maciejmiklas/led-clock/TempSensor.h

/*
 * Licensed to the Apache Software Foundation (ASF) under one or more
 * contributor license agreements.  See the NOTICE file distributed with
 * this work for additional information regarding copyright ownership.
 * The ASF licenses this file to You under the Apache License, Version 2.0
 * (the "License"); you may not use this file except in compliance with
 * the License.  You may obtain a copy of the License at
 *
 *      http://www.apache.org/licenses/LICENSE-2.0
 *
 * Unless required by applicable law or agreed to in writing, software
 * distributed under the License is distributed on an "AS IS" BASIS,
 * WITHOUT WARRANTIES OR CONDITIONS OF ANY KIND, either express or implied.
 * See the License for the specific language governing permissions and
 * limitations under the License.
 */
#ifndef TEMPSENSOR_H_
#define TEMPSENSOR_H_

#include "Arduino.h"
#include "OneWire.h"
#include "DallasTemperature.h"
#include "ArdLog.h"
#include "DispUtil.h"

class TempSensor {
public:
	TempSensor();
	float getTemp();
	void cycle();

private:
	constexpr static float READ_ADJUST = 0.0f;
	const static uint8_t DIG_PIN_TEMP_SENSOR = 44;
	const static uint16_t PROBE_FREQ_MS = 10000;

	float curentTemp;
	uint32_t lastProbeTime;
	OneWire oneWire;
	DallasTemperature dallasTemperature;

	inline void readTemp();
	void init();
};

#endif /* TEMPSENSOR_H_ */
