maciejmiklas/led-clock/WeatherDisplay.cpp

/*
 * Licensed to the Apache Software Foundation (ASF) under one or more
 * contributor license agreements.  See the NOTICE file distributed with
 * this work for additional information regarding copyright ownership.
 * The ASF licenses this file to You under the Apache License, Version 2.0
 * (the "License"); you may not use this file except in compliance with
 * the License.  You may obtain a copy of the License at
 *
 *      http://www.apache.org/licenses/LICENSE-2.0
 *
 * Unless required by applicable law or agreed to in writing, software
 * distributed under the License is distributed on an "AS IS" BASIS,
 * WITHOUT WARRANTIES OR CONDITIONS OF ANY KIND, either express or implied.
 * See the License for the specific language governing permissions and
 * limitations under the License.
 */
#include "WeatherDisplay.h"

PROGMEM const uint8_t WEATHER_ICON[WEATHER_ICON_SIZE][FONT8_HEIGHT] = {
// ICON_IDX_MIX_SUN_RAIN
		{ B00000000, B00000000, B00000000, B00000000, B00000001, B00000010, B00000010, B00000100 }, //
		{ B00010000, B00001000, B00000100, B11110001, B00001111, B00000001, B00000001, B00000000 }, //
		{ B10000100, B10001000, B00010000, B11000000, B11100000, B11110110, B11110000, B11100000 }, //
//
		{ B00001000, B00001000, B00000111, B00000000, B00000000, B00000001, B00000000, B00000001 }, //
		{ B00000000, B00000000, B10101010, B01010100, B10101000, B01010000, B10000000, B00000000 }, //
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
	case 0:
		iconOffset = ICON_IDX_MIX_SUN_RAIN;
		break;

	case 1:
		iconOffset = ICON_IDX_PARTLY_SUNNY;
		break;

	case 2:
		iconOffset = ICON_IDX_RAIN;
		break;

	case 3:
		iconOffset = ICON_IDX_THUNDERSTORM;
		break;

	case 4:
		iconOffset = ICON_IDX_MIX_SUN_THUNDERSTORM;
		break;

	case 5:
		iconOffset = ICON_IDX_MOON;
		break;

	case 6:
		iconOffset = ICON_IDX_MIX_SUN_SNOW;
		break;

	case 7:
		iconOffset = ICON_IDX_SNOW;
		break;

	case 8:
		iconOffset = ICON_IDX_CLOUDY;
		break;

	case 9:
		iconOffset = ICON_IDX_SUNNY;
		break;

	default:
		iconOffset = ICON_EMPTY;
		break;
	}

	if (iconOffset != lastIcon) {
		copyIconData(iconOffset);
		lastIcon = iconOffset;
	}
}

void inline WeatherDisplay::copyIconData(uint8_t iconIdx) {
	uint8_t iconEnd = iconIdx + ICON_BYTES;
	uint8_t dataRowOffset = 0;
	uint8_t dataCol = 0;
	uint8_t dispRowBytesIdx = 0;
	for (; iconIdx < iconEnd; iconIdx++) {
		if (dispRowBytesIdx == ICON_ROW_BYTES) {
			dataRowOffset += KIT_DIM;
			dataCol = 0;
		}
		for (uint8_t kitRow = 0; kitRow < KIT_DIM; kitRow++) {
			uint8_t dataRow = kitRow + dataRowOffset;
			uint8_t data = pgm_read_byte(&WEATHER_ICON[iconIdx][kitRow]);
			iconData[dataRow][dataCol] = data;
#if LOG_LC
			log(F("YW I: (%d,%d) = (%d,%d) = %d"), dataRow, dataCol, iconIdx, kitRow, data);
#endif
		}
		dataCol++;
		dispRowBytesIdx++;
	}

	canvas->paint(ICON_START_X_PX, ICON_START_Y_PX, ICON_WIDTH_PX, ICON_HEIGHT_PX, iconData);
}

void WeatherDisplay::refreshCodes() {
	codesReadSize = serialAPI->getWeather_codes(codes, CODES_SIZE);
	codesIxd = 0;
	if (codesReadSize == 0) {
		weatherRefreshMs = WEATHER_REFRESH_ON_ERROR_MS;
	} else {
		weatherRefreshMs = WEATHER_REFRESH_MS;
	}
}

void WeatherDisplay::refreshWeatherText(boolean force) {
	if (!force && !serialAPI->getWeather_textChange()) {
		return;
	}

	cleanCharArray(buf, TEXT_BUFFER_SIZE);
	uint8_t idx = append(buf, 0, TEXT_BUFFER_MAX_SIZE, serialAPI->getWeather_text());
	buf[idx++] = '\0';

#if LOG_LC
	log(F("YW T(%d):"), idx);
	logs(buf, TEXT_BUFFER_SIZE);
#endif

	weatherTextArea.scroll(0, 16, ScrollingText8x8::CONTINOUS_LOOP, buf);
}

uint8_t inline WeatherDisplay::sep(uint8_t idx, uint8_t chars) {
	for (uint8_t i = 0; i < chars; i++) {
		buf[idx++] = ' ';
	}
	return idx;
}

void WeatherDisplay::init() {
	refreshWeatherText(true);
	refreshCodes();
	refreshIcon();
}

void WeatherDisplay::refreshWeather() {
	uint32_t time = ms();
	if (time - lastWeatherRefreshMs > weatherRefreshMs) {
		lastWeatherRefreshMs = time;
		refreshWeatherText(false);
		refreshCodes();
	}
}

void WeatherDisplay::cycle() {
	weatherTextArea.cycle();

	refreshWeather();
	refreshIcon();
}
