maciejmiklas/led-clock/LEDClock.h

#ifndef LEDCLOCK_H_
#define LEDCLOCK_H_

#include "Arduino.h"
#include "ArdLog.h"
#include "Display.h"
#include "ScrollingText8x8.h"
#include "DateTimeDisplay.h"
#include "WeatherDisplay.h"
#include "SerialAPI.h"
#include "Brightness.h"
#include "TempSensor.h"
#include "TempSensorDriver.h"

#endif /* LEDCLOCK_H_ */
